apriebeMTU/Hibernacula-Wireless-Sensor-Network/Repeater/00_ICSP/00_ICSP_Test/00_ICSP_Test.ino

// Title: 
// Author: Alex Riebe
// Description: This program tests the functionality



const uint8_t  LED_PIN{8};

void setup() {
  // put your setup code here, to run once:
    pinMode(LED_PIN, OUTPUT);

}

void loop() {
  // put your main code here, to run repeatedly:
  digitalWrite(LED_PIN, HIGH);   
  delay(1000);   
  digitalWrite(LED_PIN, LOW);   
  delay(1000);
}
